apfelaudio/eurorack-pmod/gateware/cores/sampler.sv

// Sample player.
//
// Given an input trigger on input 0, play converted .wav sample on output 0.
//
// At the moment this is VERY simple and uses a hex file put straight into the FPGA
// RAM, but it should be pretty easy to store it in the SPI flash (which
// has a lot more space).
//
// Mapping:
// - Input 0: Trigger input
// - Output 0: Sample audio output

module sampler #(
    parameter W = 16,
    parameter FP_OFFSET = 2,
    parameter N_SAMPLES = 12'h690,
    parameter PATH_SAMPLES = "cores/util/sampler_data/clap.hex"
)(
    input rst,
    input clk,
    input strobe,
    input signed [W-1:0] sample_in0,
    input signed [W-1:0] sample_in1,
    input signed [W-1:0] sample_in2,
    input signed [W-1:0] sample_in3,
    output signed [W-1:0] sample_out0,
    output signed [W-1:0] sample_out1,
    output signed [W-1:0] sample_out2,
    output signed [W-1:0] sample_out3,
    input [7:0] jack
);

`define FROM_MV(value) (value <<< FP_OFFSET)

// Input trigger voltage thresholds.
localparam TRIGGER_HI = `FROM_MV(1000);

// RAM containing the sample itself
logic [W-1:0] wav_samples [0:N_SAMPLES];
initial $readmemh(PATH_SAMPLES, wav_samples);

// Playback speed is a bit slower than sample_clk.
logic [W-1:0] sclkdiv = 16'h0;
// Current index in the sample we are playing.
logic [$clog2(N_SAMPLES):0] sample_pos = 0;
// Value of the last sample at sample_pos, synchronized to sample_clk.
logic [W-1:0] cur_sample = 16'h0;

always_ff @(posedge clk) begin
    if (strobe) begin
        sclkdiv <= sclkdiv + 1;
        if (sclkdiv % 2 == 0 && sample_pos <= N_SAMPLES) begin
            sample_pos <= sample_pos + 1;
        end
        if (sample_in0 < TRIGGER_HI) begin
            // Hold first sample as long as we have no trigger. As
            // soon as it goes high, we 'allow' playback.
            sample_pos <= 0;
        end
        if (sample_pos < N_SAMPLES) begin
            cur_sample <= wav_samples[sample_pos[$clog2(N_SAMPLES)-1:0]];
        end else begin
            // If we go past the end of the sample, hold 0V at the output.
            cur_sample <= 16'h0;
        end
    end
end


assign sample_out0 = cur_sample;

assign sample_out1 = sample_in1;
assign sample_out2 = sample_in2;
assign sample_out3 = sample_in3;

endmodule
