apfelaudio/eurorack-pmod/gateware/cores/vca.sv

// Precision multiplier (VCA with polarization)
//
// Given an input voltage, multiply input audio by input voltage. This VCA
// performs polarization so negative voltages will also amplify, but with
// inverted phase. Both inputs are audio rate.
//
// Mapping:
// - Input 0: Gain input #1
// - Input 1: Signal input #1
// - Input 2: Gain input #2
// - Input 3: Signal input #2
// - Output 0: Input #1 (mirrored)
// - Output 1: Input 0 * Input 1
// - Output 2: Input #3 (mirrored)
// - Output 3: Input 2 * Input 3
//
module vca #(
    parameter W = 16
)(
    input rst,
    input clk,
    input strobe,
    input signed [W-1:0] sample_in0,
    input signed [W-1:0] sample_in1,
    input signed [W-1:0] sample_in2,
    input signed [W-1:0] sample_in3,
    output signed [W-1:0] sample_out0,
    output signed [W-1:0] sample_out1,
    output signed [W-1:0] sample_out2,
    output signed [W-1:0] sample_out3,
    input [7:0] jack
);

logic signed [(W*2)-1:0] vca1;
logic signed [(W*2)-1:0] vca2;

assign vca1 = sample_in0 * sample_in1;
assign vca2 = sample_in2 * sample_in3;

assign sample_out0 = sample_in0;
assign sample_out1 = W'(vca1 >>> W);
assign sample_out2 = sample_in2;
assign sample_out3 = W'(vca2 >>> W);

endmodule
