apfelaudio/eurorack-pmod/gateware/util/uart_baud_tick_gen.v

/*
 *  icebreaker examples - Async uart baud tick generator module
 *
 *  Copyright (C) 2018 Piotr Esden-Tempski <piotr@esden.net>
 *
 *  Permission to use, copy, modify, and/or distribute this software for any
 *  purpose with or without fee is hereby granted, provided that the above
 *  copyright notice and this permission notice appear in all copies.
 *
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
 */

/***
 * This module generates a bit baud tick multiplied by the oversampling parameter.
 */
module baud_tick_gen(
	input clk, enable,
	output tick);
parameter clk_freq = 12000000;
parameter baud     =   115200;
parameter oversampling = 1;

function integer log2(input integer v); begin log2=0; while(v >> log2) log2 = log2 + 1; end endfunction

localparam acc_width = log2(clk_freq / baud) + 8; // +/- 2% max timing error over a byte

reg [acc_width:0] acc = 0;

localparam shiftlimiter = log2((baud * oversampling) >> (31 - acc_width)); // this makes sure inc calculation doesn't overflow (verilog uses 32bit variables internally)
localparam inc = ((baud * oversampling << (acc_width - shiftlimiter)) + (clk_freq >> (shiftlimiter + 1))) / (clk_freq >> shiftlimiter); // Calculate accumulate increment
//initial $display("acc_width %d, shiftlimit %d, inc %d", acc_width, shiftlimiter, inc);

always @(posedge clk) if (enable) acc <= acc[acc_width-1:0] + inc[acc_width:0]; else acc <= inc[acc_width:0];
assign tick = acc[acc_width];

endmodule
